hedfd434/5V_boost_module_MCP/images/IMG_3020.jpeg

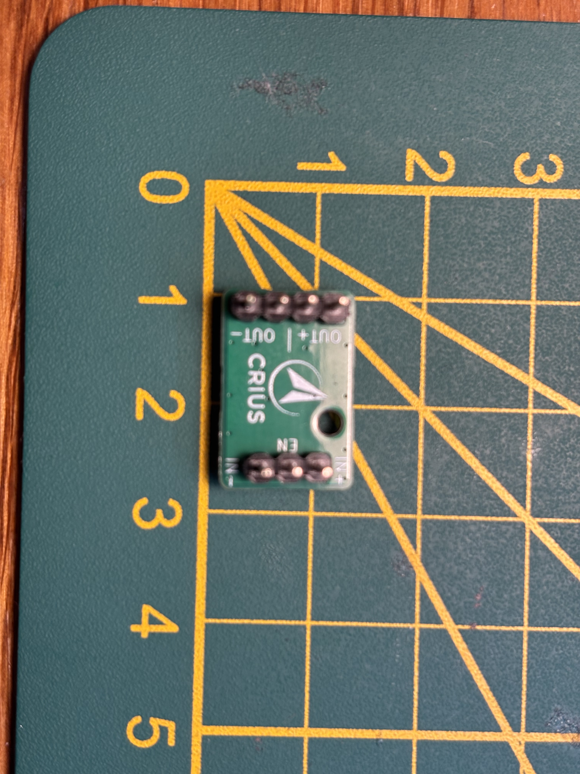
images/IMG_3020.jpeg
